eharvester/toastershield/src/PIDparams.h

// PID Parameters 
// adjust the parameters to get smooth temperature control
// values depend on size of oven, power of heater, airflow, insulation aso.
// must be adjusted only once
double Kp=20.0, Ki=0.01, Kd=5.0;
