eharvester/toastershield/src/lcdsymbols.h

#define EMPTYBAR_SIZEX 128
#define EMPTYBAR_SIZEY 8

#define FULLBARSTEP_SIZEX 8
#define FULLBARSTEP_SIZEY EMPTYBAR_SIZEY


#define EIGHT0x81 0x81,0x81,0x81,0x81,0x81,0x81,0x81,0x81
const PROGMEM unsigned char emptybar[] = 
{0xFF,0x81,0x81,0x81,0x81,0x81,0x81,0x81,EIGHT0x81,EIGHT0x81,EIGHT0x81,EIGHT0x81,EIGHT0x81,EIGHT0x81,EIGHT0x81,EIGHT0x81,EIGHT0x81,EIGHT0x81,EIGHT0x81,EIGHT0x81,EIGHT0x81,EIGHT0x81,0x81,0x81,0x81,0x81,0x81,0x81,0x81,0xFF};

#define FULLBARSTEP_SIZEX 8
#define FULLBARSTEP_SIZEY EMPTYBAR_SIZEY

const PROGMEM unsigned char fullbarstep[] = 
{0xFF,0xFF,0xFF,0xFF,0xFF,0xFF,0xFF,0xFF};

const PROGMEM unsigned char HeaterSymbol16x16[] = {
0x00, 0x38, 0xFE, 0xC7, 0x01, 0x00, 0x38, 0xFE, 0xC7, 0x01, 0x00, 0x38, 0xFE, 0xC7, 0x01, 0x00,
0x00, 0xA0, 0xB8, 0x9F, 0x87, 0x80, 0xA0, 0xB8, 0x9F, 0x87, 0x80, 0xA0, 0xB8, 0x9F, 0x87, 0x00
};

const PROGMEM unsigned char FanSymbol16x16[] = {
0x18, 0x9C, 0x8C, 0x9C, 0xB8, 0xF3, 0xE3, 0x7F, 0x7E, 0xE0, 0xF0, 0xBB, 0x9F, 0x8E, 0xE0, 0xE0,
0x07, 0x07, 0x71, 0xF9, 0xDD, 0x0F, 0x07, 0x7E, 0xFE, 0xC7, 0xCF, 0x1D, 0x39, 0x31, 0x39, 0x18
};

const PROGMEM unsigned char EmptySymbol16x16[] = {
0x00, 0x00, 0x00, 0x00, 0x00, 0x00, 0x00, 0x00, 0x00, 0x00, 0x00, 0x00, 0x00, 0x00, 0x00, 0x00,
0x00, 0x00, 0x00, 0x00, 0x00, 0x00, 0x00, 0x00, 0x00, 0x00, 0x00, 0x00, 0x00, 0x00, 0x00, 0x00
};

const PROGMEM unsigned char logo [] = {
0x00, 0x00, 0x00, 0x00, 0x00, 0xFC, 0xFF, 0x07, 0x03, 0x01, 0x00, 0x00, 0x00, 0x01, 0x01, 0x0E,
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
0xFF, 0xFF, 0xE0, 0xC0, 0x80, 0x80, 0x80, 0x80, 0x80, 0xC0, 0x80, 0x00, 0x00, 0xFF, 0xFF, 0xFF,
0x03, 0x03, 0x03, 0x07, 0xFF, 0xFF, 0xFE, 0x00, 0x00, 0x7C, 0xFE, 0xFF, 0xDB, 0x9B, 0x9B, 0x9B,
0x9F, 0x9F, 0x1E, 0x00, 0x00, 0xFF, 0xFF, 0xFF, 0x03, 0x03, 0x03, 0x03, 0x00, 0x00, 0x00, 0x00,
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
};
